machdyne/eis/firmware/eis/eis_tinyusb.h

/* 
 * The MIT License (MIT)
 *
 * Copyright (c) 2019 Ha Thach (tinyusb.org)
 *
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
 * This file is based on code from the TinyUSB stack.
 */

#define TU_BIT(n)             (1UL << (n))

/// Standard HID Boot Protocol Keyboard Report.
typedef struct TU_ATTR_PACKED
{
  uint8_t modifier;   /**< Keyboard modifier (KEYBOARD_MODIFIER_* masks). */
  uint8_t reserved;   /**< Reserved for OEM use, always set to 0. */
  uint8_t keycode[6]; /**< Key codes of the currently pressed keys. */
} hid_keyboard_report_t;

/// Keyboard modifier codes bitmap
typedef enum
{
  KEYBOARD_MODIFIER_LEFTCTRL   = TU_BIT(0), ///< Left Control
  KEYBOARD_MODIFIER_LEFTSHIFT  = TU_BIT(1), ///< Left Shift
  KEYBOARD_MODIFIER_LEFTALT    = TU_BIT(2), ///< Left Alt
  KEYBOARD_MODIFIER_LEFTGUI    = TU_BIT(3), ///< Left Window
  KEYBOARD_MODIFIER_RIGHTCTRL  = TU_BIT(4), ///< Right Control
  KEYBOARD_MODIFIER_RIGHTSHIFT = TU_BIT(5), ///< Right Shift
  KEYBOARD_MODIFIER_RIGHTALT   = TU_BIT(6), ///< Right Alt
  KEYBOARD_MODIFIER_RIGHTGUI   = TU_BIT(7)  ///< Right Window
}hid_keyboard_modifier_bm_t;
