machdyne/eis/firmware/eis/keycode2scancode.h

static uint8_t keycode2scancode[] = {
	0x00,
	0x00,
	0x00,
	0x00,
	0x1C,
	0x32,
	0x21,
	0x23,
	0x24,
	0x2B,
	0x34,
	0x33,
	0x43,
	0x3B,
	0x42,
	0x4B,
	0x3A,
	0x31,
	0x44,
	0x4D,
	0x15,
	0x2D,
	0x1B,
	0x2C,
	0x3C,
	0x2A,
	0x1D,
	0x22,
	0x35,
	0x1A,
	0x16,
	0x1E,
	0x26,
	0x25,
	0x2E,
	0x36,
	0x3D,
	0x3E,
	0x46,
	0x45,
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
};
